sudo-apt-install-tap/ErgoSplit/Images/Right sch.png

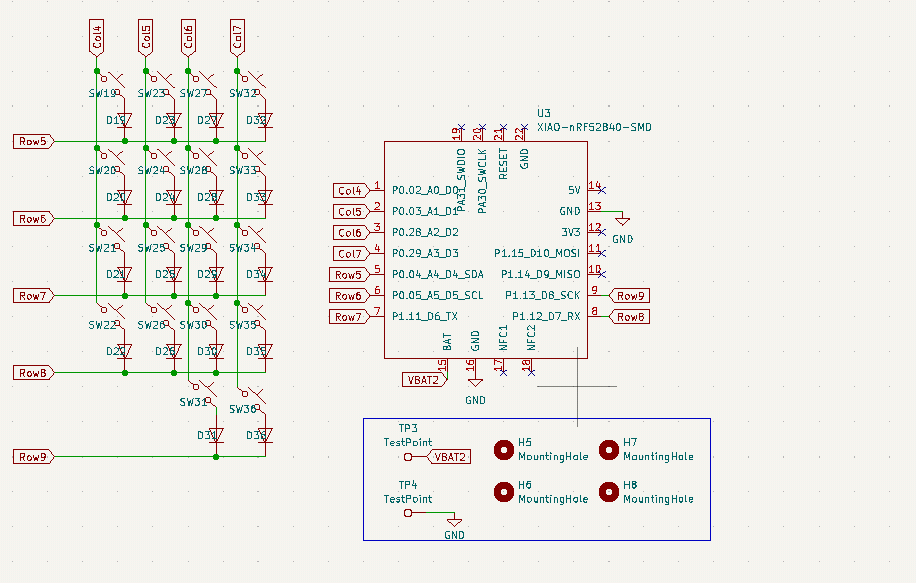
Images/Right sch.png
